hfvermeer/retro_xmas_gadget/kicad/3d-models/KB3SPRS.STEP

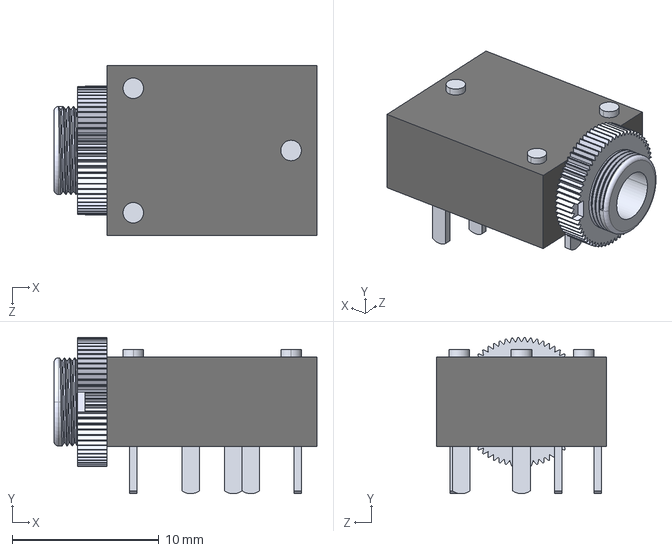
[picture p15: CAD file, 2025-10-25]
kicad/3d-models/KB3SPRS.STEP
17.9 x 10.6 x 11.6 mm
