hfvermeer/retro_xmas_gadget/kicad/3d-models/10114830-10103LF.step

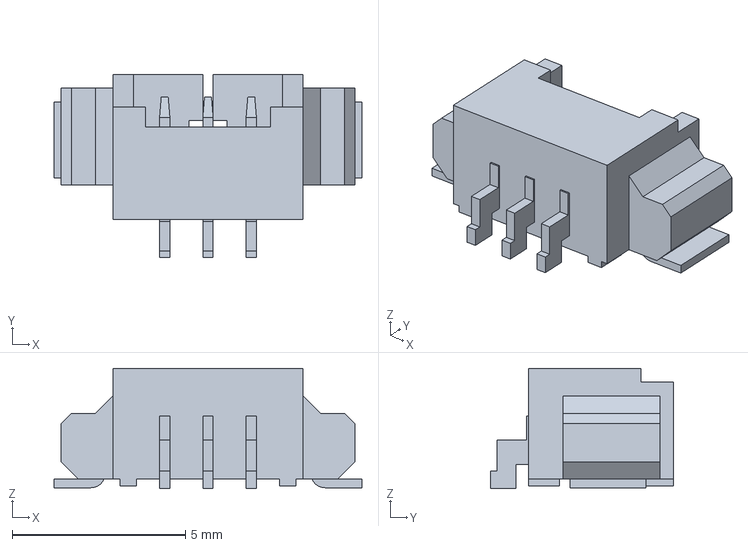
[picture p16: CAD file, 2025-10-30]
kicad/3d-models/10114830-10103LF.step
8.90 x 5.30 x 3.48 mm
