hfvermeer/retro_xmas_gadget/kicad/3d-models/10114830-10102LF.step

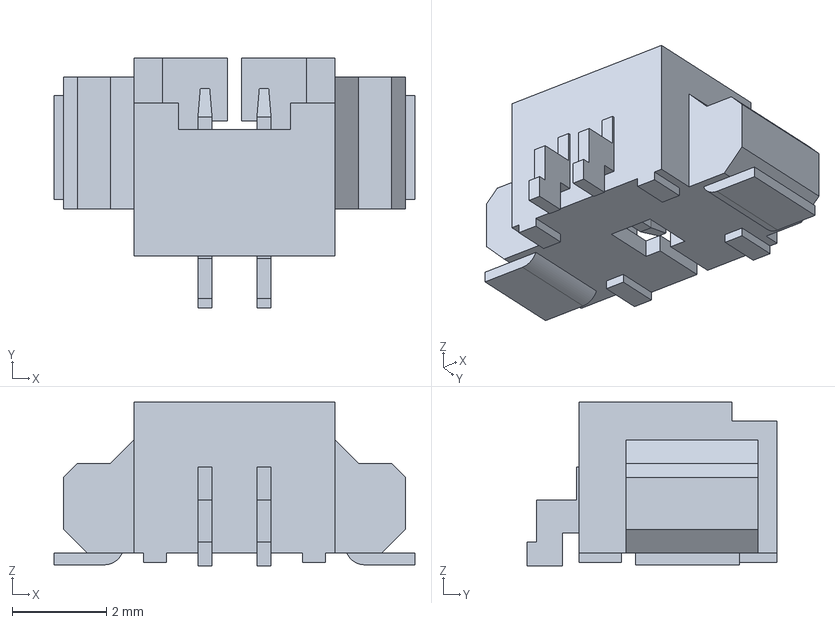
[picture p17: CAD file, 2025-10-30]
kicad/3d-models/10114830-10102LF.step
7.65 x 5.30 x 3.48 mm
