hfvermeer/retro_xmas_gadget/kicad/3d-models/2041021-4.stp

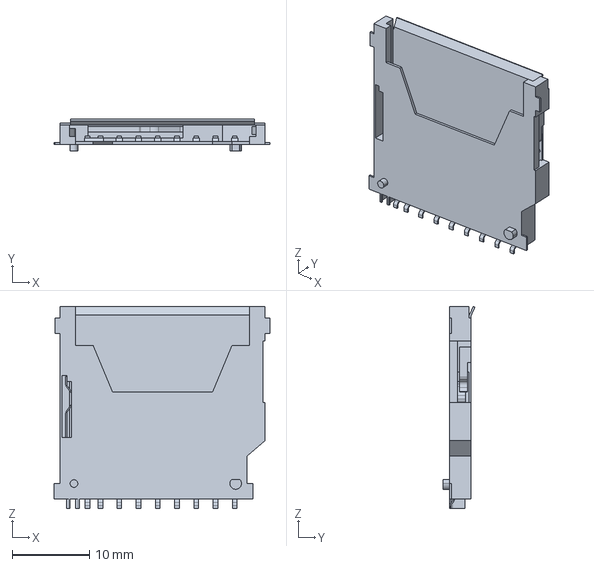
[picture p18: CAD file, 2025-10-25]
kicad/3d-models/2041021-4.stp
28.0 x 4.15 x 26.2 mm
